naka6ryo/Gricon_Controller-s_Code/Hardware/aaa-battery--2/Renderings/untitled.9.jpg

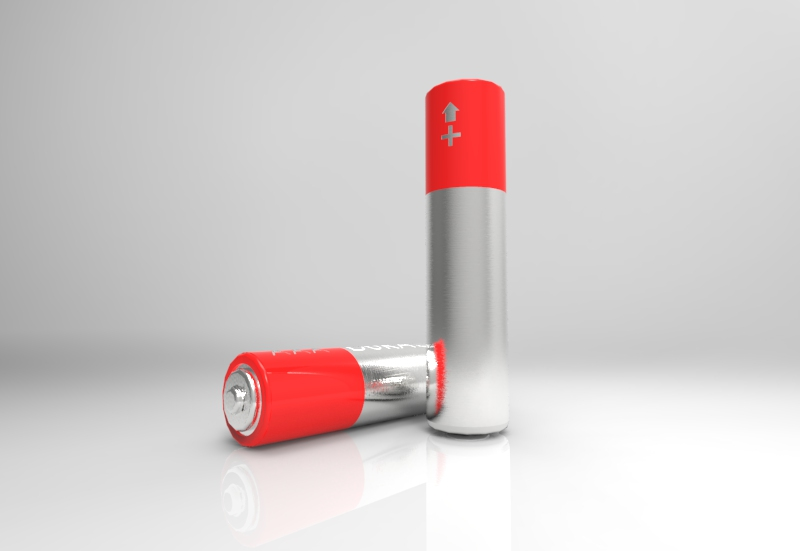
Hardware/aaa-battery--2/Renderings/untitled.9.jpg
