naka6ryo/Gricon_Controller-s_Code/Hardware/cad-8-pin-header-1.snapshot.2/vlc_ReZSubCM5v.gif

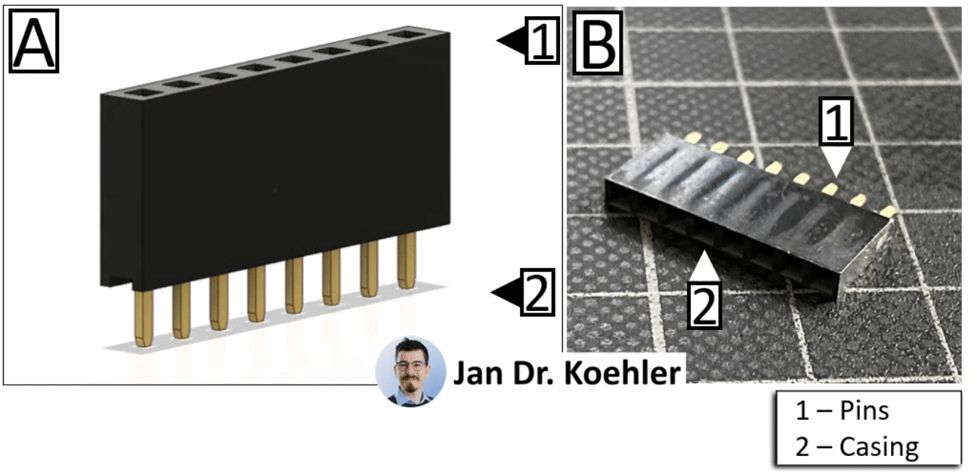
Hardware/cad-8-pin-header-1.snapshot.2/vlc_ReZSubCM5v.gif
