naka6ryo/Gricon_Controller-s_Code/Hardware/male-header-pins-1.snapshot.11/Male Header Pin Config.STEP

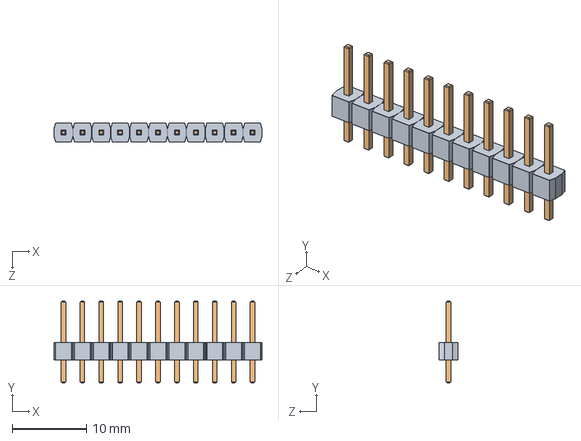
[picture p20: CAD file, 2026-01-13]
Hardware/male-header-pins-1.snapshot.11/Male Header Pin Config.STEP
27.9 x 10.9 x 2.54 mm
Spacer x 11
Male Header Pin x 11
