naka6ryo/Gricon_Controller-s_Code/Hardware/bluetooth-module-hc-05-1.snapshot.4/Bluetooth Module HC-05/HC-05 part8.SLDPRT

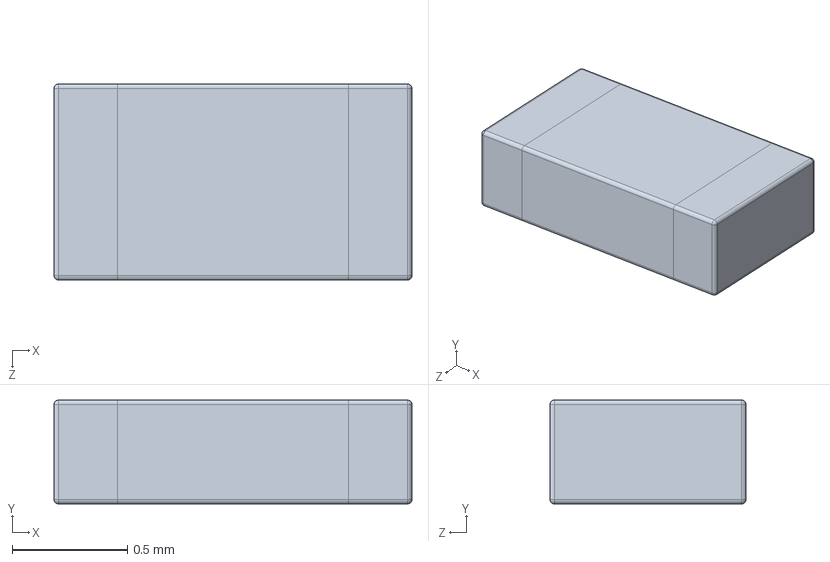
[picture p21: CAD file, 2026-01-13]
Hardware/bluetooth-module-hc-05-1.snapshot.4/Bluetooth Module HC-05/HC-05 part8.SLDPRT
1.55 x 0.45 x 0.85 mm
