naka6ryo/Gricon_Controller-s_Code/Hardware/for 3Dprints/done/Body04.stl

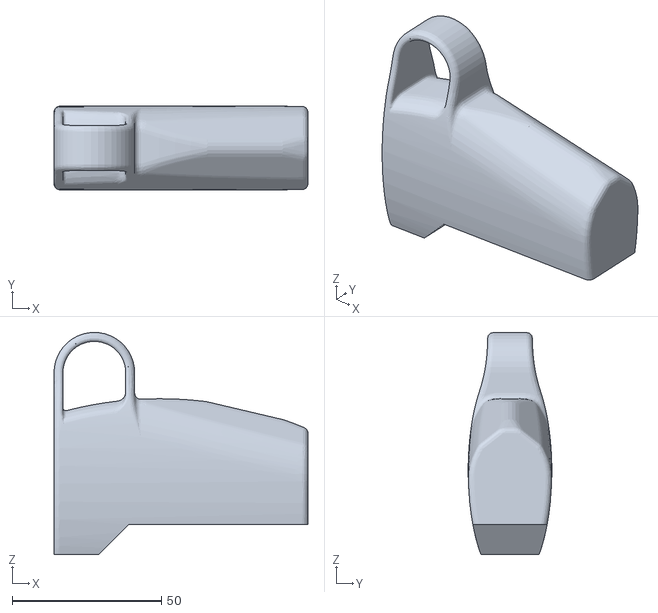
[picture p22: CAD file, 2026-01-13]
Hardware/for 3Dprints/done/Body04.stl
85.0 x 28.0 x 74.3
