naka6ryo/Gricon_Controller-s_Code/Hardware/for 3Dprints/done/Body02.stl

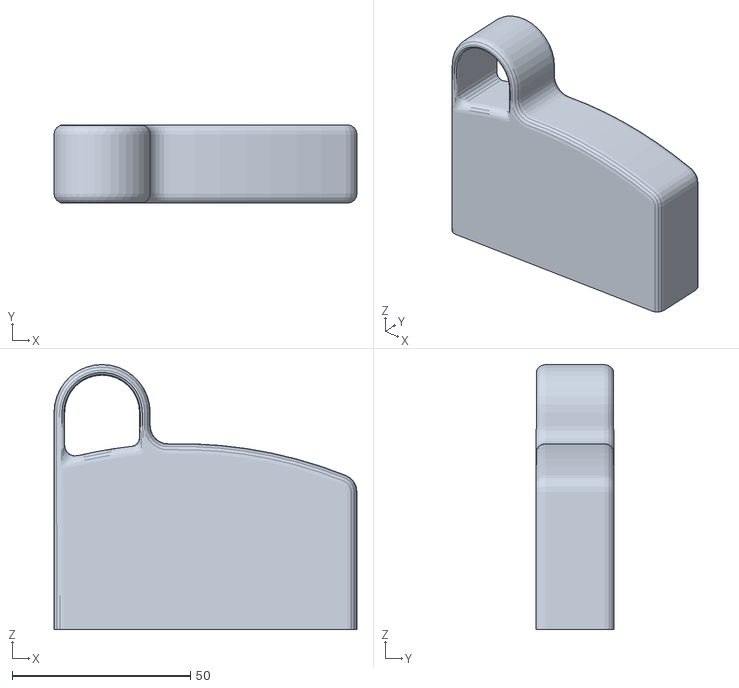
[picture p23: CAD file, 2026-01-13]
Hardware/for 3Dprints/done/Body02.stl
85.0 x 22.0 x 74.3
