naka6ryo/Gricon_Controller-s_Code/Hardware/bluetooth-module-hc-05-1.snapshot.4/Bluetooth Module HC-05/HC-05 part1.SLDPRT

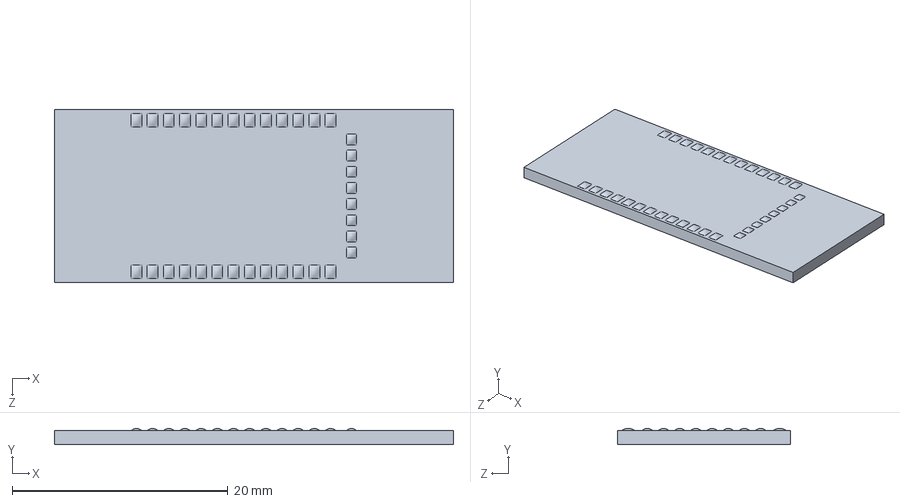
[picture p24: CAD file, 2026-01-13]
Hardware/bluetooth-module-hc-05-1.snapshot.4/Bluetooth Module HC-05/HC-05 part1.SLDPRT
37.0 x 1.51 x 16.0 mm
