naka6ryo/Gricon_Controller-s_Code/Hardware/bluetooth-module-hc-05-1.snapshot.4/Bluetooth Module HC-05/HC-05 part10.SLDPRT

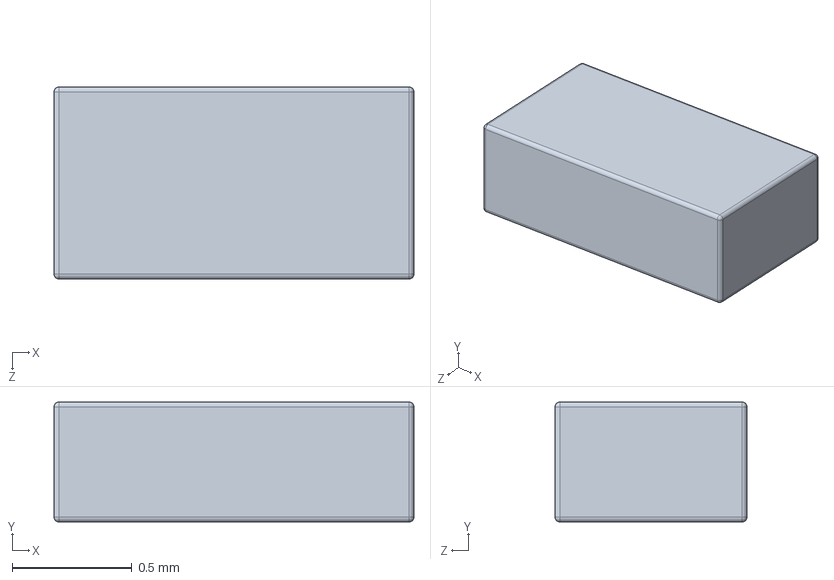
[picture p25: CAD file, 2026-01-13]
Hardware/bluetooth-module-hc-05-1.snapshot.4/Bluetooth Module HC-05/HC-05 part10.SLDPRT
1.50 x 0.5 x 0.8 mm
