naka6ryo/Gricon_Controller-s_Code/Hardware/bluetooth-module-hc-05-1.snapshot.4/Bluetooth Module HC-05/HC-05 part5.SLDPRT

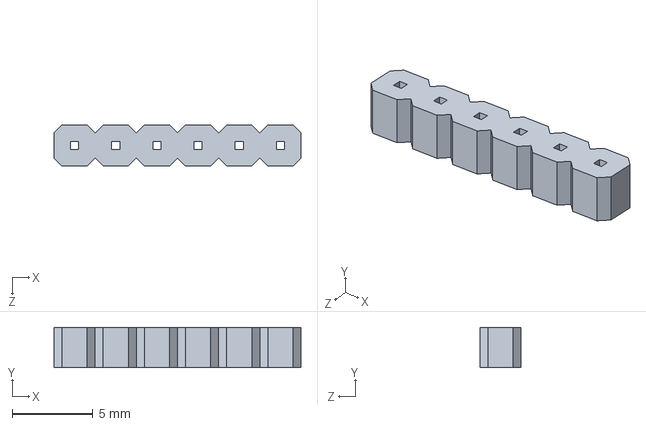
[picture p26: CAD file, 2026-01-13]
Hardware/bluetooth-module-hc-05-1.snapshot.4/Bluetooth Module HC-05/HC-05 part5.SLDPRT
15.3 x 2.50 x 2.55 mm
