naka6ryo/Gricon_Controller-s_Code/Hardware/bluetooth-module-hc-05-1.snapshot.4/Bluetooth Module HC-05/HC-05 part4.SLDPRT

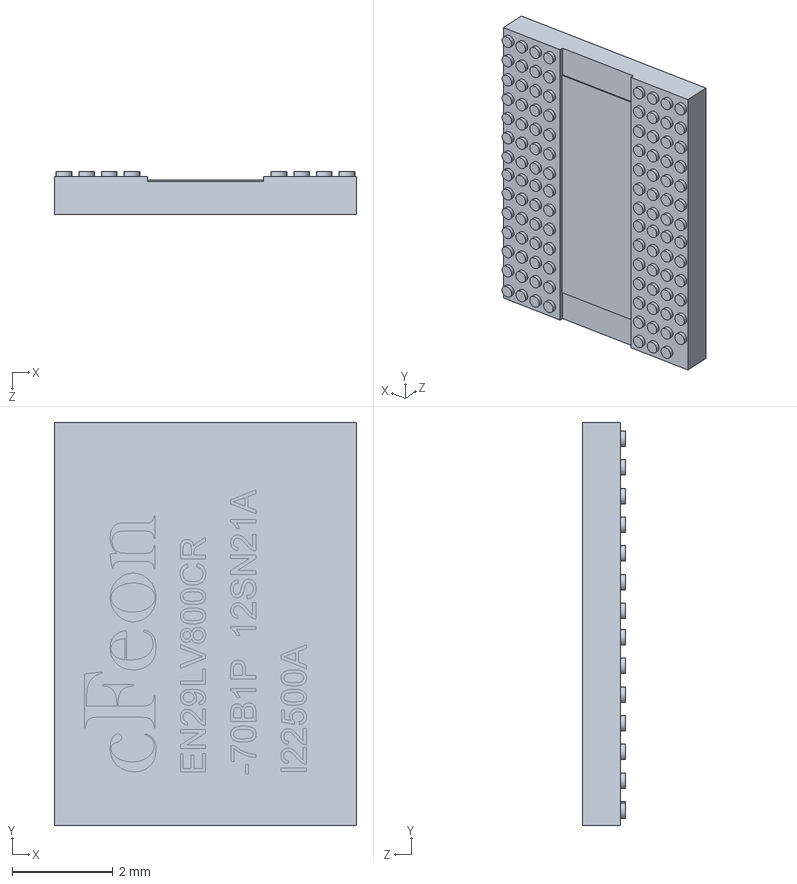
[picture p27: CAD file, 2026-01-13]
Hardware/bluetooth-module-hc-05-1.snapshot.4/Bluetooth Module HC-05/HC-05 part4.SLDPRT
6.00 x 8.00 x 0.85 mm
