naka6ryo/Gricon_Controller-s_Code/Hardware/Assembly.png

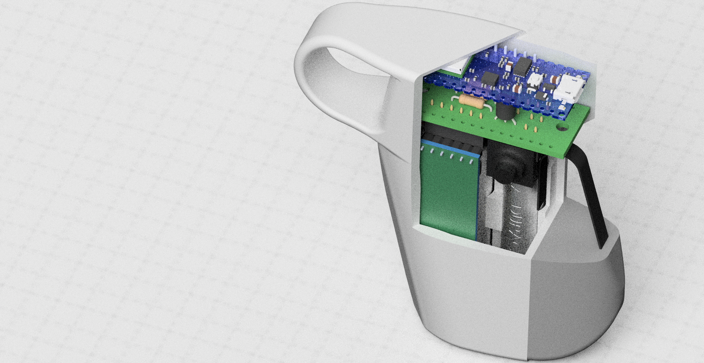
Hardware/Assembly.png
